eldar6776/hotel-access-system-1/fw/EntryDoor/DE-060718/Src/rc522.c

/**
 ******************************************************************************
 * File Name          : mfrc522.c
 * Date               : 28/02/2016 23:16:19
 * Description        : mifare RC522 software modul
 ******************************************************************************
 *
 *
 ******************************************************************************
 */


/* Includes ------------------------------------------------------------------*/
#include "main.h"
#include "rc522.h"
#include "common.h"


/* Imported Type  ------------------------------------------------------------*/
extern UART_HandleTypeDef huart1;


/* Imported Variable  --------------------------------------------------------*/
/* Imported Function  --------------------------------------------------------*/
/* Private Define ------------------------------------------------------------*/
#define DEFAULT_SYSTEM_ID					0xABCDU
#define RC522_CARD_VALID_EVENT_TIME			3210U   // 3 s reader unlisten time after card read
#define RC522_CARD_INVALID_EVENT_TIME		987U    // ~1 s reader unlisten time after card read
#define RC522_POWER_ON_DELAY_TIME           8901U	// 8 s on power up reader is disbled 
#define RC522_PROCESS_TIME					123U	// 123 ms read rate
#define RC522_BUFF_LEN						16U     // buffer byte lenght
#define RC522_READ    						0x7FU	// RC522 i2c read address
#define RC522_WRITE   						0x7EU	// RC522 i2c write address
#define RC522_TIMEOUT						20U     // RC522 i2c 5 ms transfer time_mout limit
#define RC522_TRIALS						50U		// RC522 i2c 100 time_ms operation retry
#define RC522_BLOCK_SIZE              		16U 
#define CARD_PENDING						0U	    // card data status type
#define CARD_VALID							0x06U	// card data status type
#define CARD_INVALID						0x15U	// card data status type
#define CARD_DATA_FORMATED					0x7FU	// card data status type
/** ==========================================================================*/
/**			M I F A R E		C A R D		S E C T O R		A D D R E S S E		  */
/** ==========================================================================*/
#define SECTOR_0							0x00U
#define SECTOR_1							0x04U
#define SECTOR_2							0x08U
#define SECTOR_3							0x0CU
#define SECTOR_4							0x10U
#define SECTOR_5							0x14U
#define SECTOR_6							0x18U
#define SECTOR_7							0x1CU
#define SECTOR_8							0x20U
/** ==========================================================================*/
/**			R C 5 2 2			C O M M A N D			L I S T				  */
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
